CharelF01/RELIP-MODBUS-SMARTY/Code/RELIP-READER/SmartReader2_2023-Mar-29_07-19-46PM-000_CustomizedView1520858296_png.png

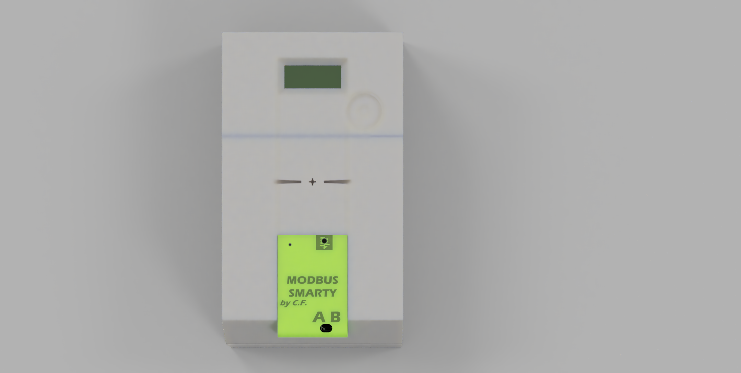
Code/RELIP-READER/SmartReader2_2023-Mar-29_07-19-46PM-000_CustomizedView1520858296_png.png
