CharelF01/RELIP-MODBUS-SMARTY/Photos/Smarty Modbus/IMG_20230321_090704.jpg

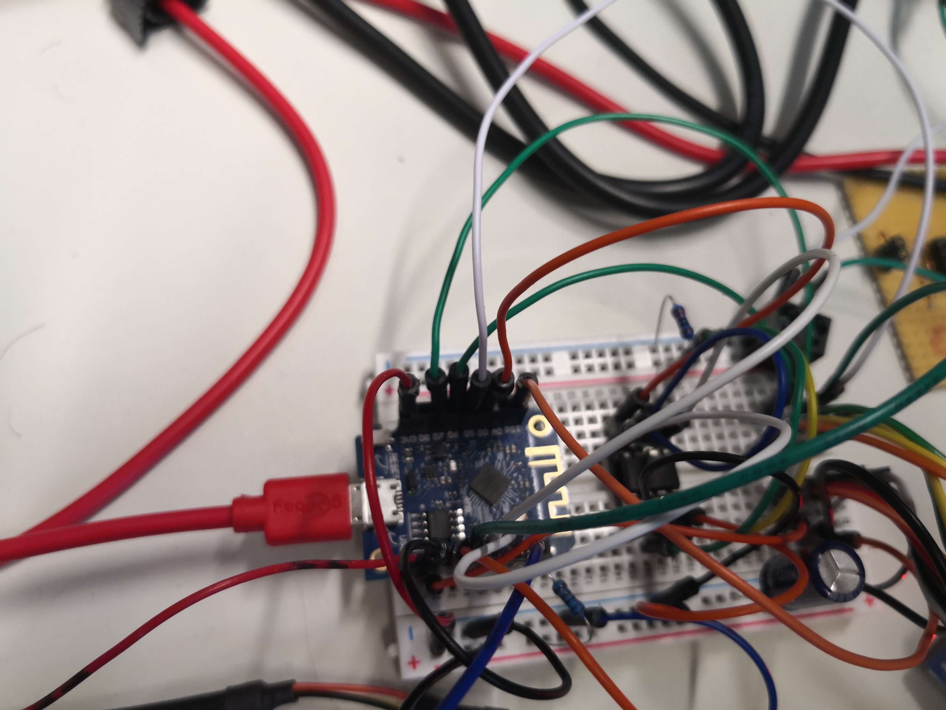
Photos/Smarty Modbus/IMG_20230321_090704.jpg
