CharelF01/RELIP-MODBUS-SMARTY/Photos/Smarty Modbus/IMG_20230321_090714.jpg

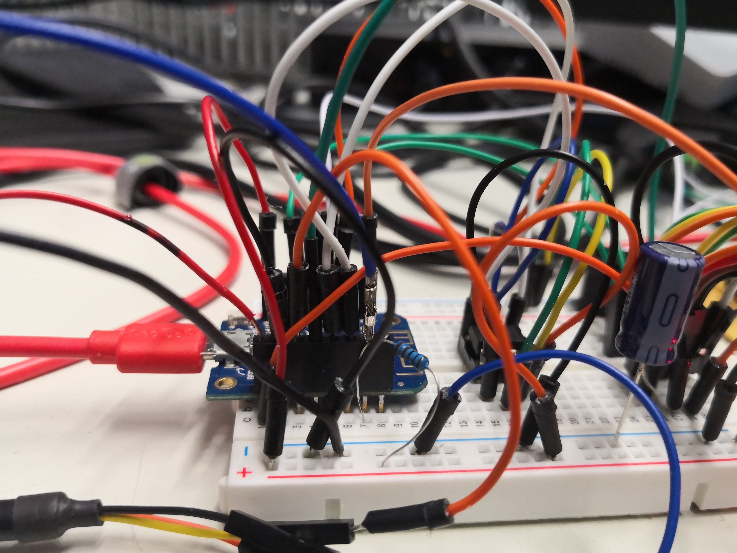
Photos/Smarty Modbus/IMG_20230321_090714.jpg
