CharelF01/RELIP-MODBUS-SMARTY/Photos/Smarty Modbus/IMG_20230323_114347.jpg

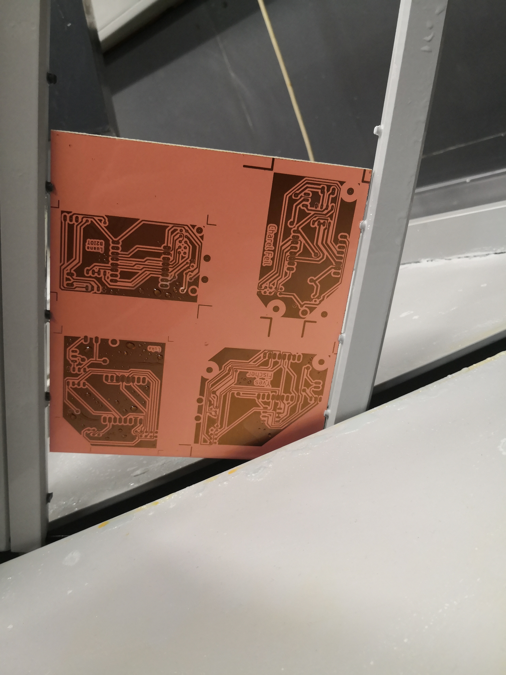
Photos/Smarty Modbus/IMG_20230323_114347.jpg
