CharelF01/RELIP-MODBUS-SMARTY/Photos/Smarty Modbus/IMG_20230323_133843.jpg

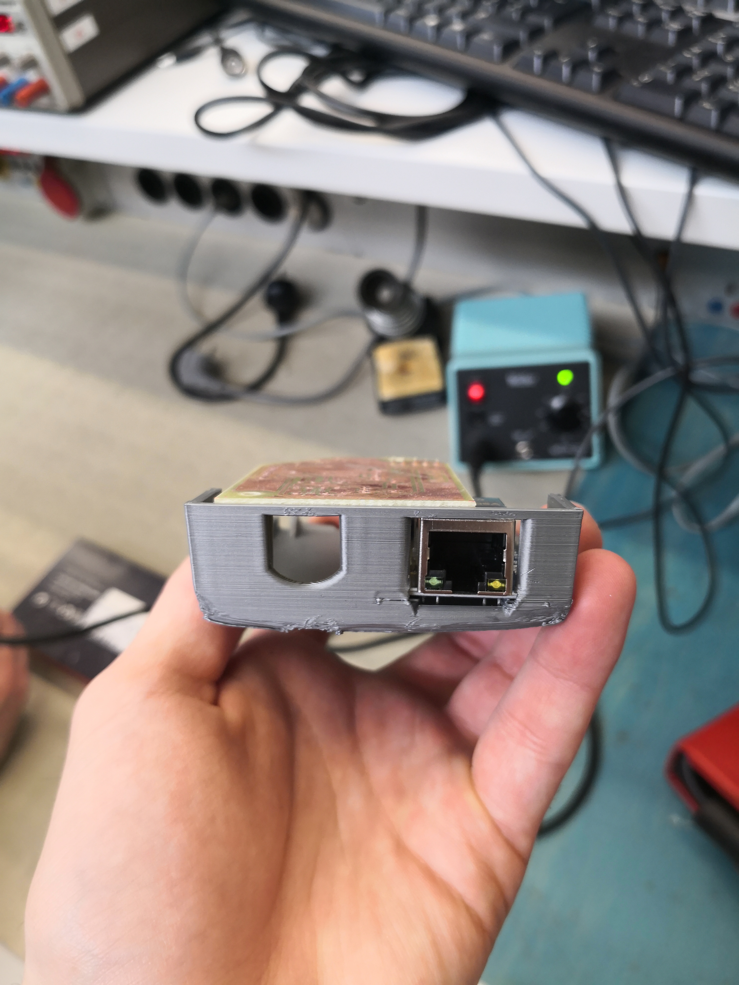
Photos/Smarty Modbus/IMG_20230323_133843.jpg
