CharelF01/RELIP-MODBUS-SMARTY/Photos/Smarty Modbus/IMG_20230324_115719.jpg

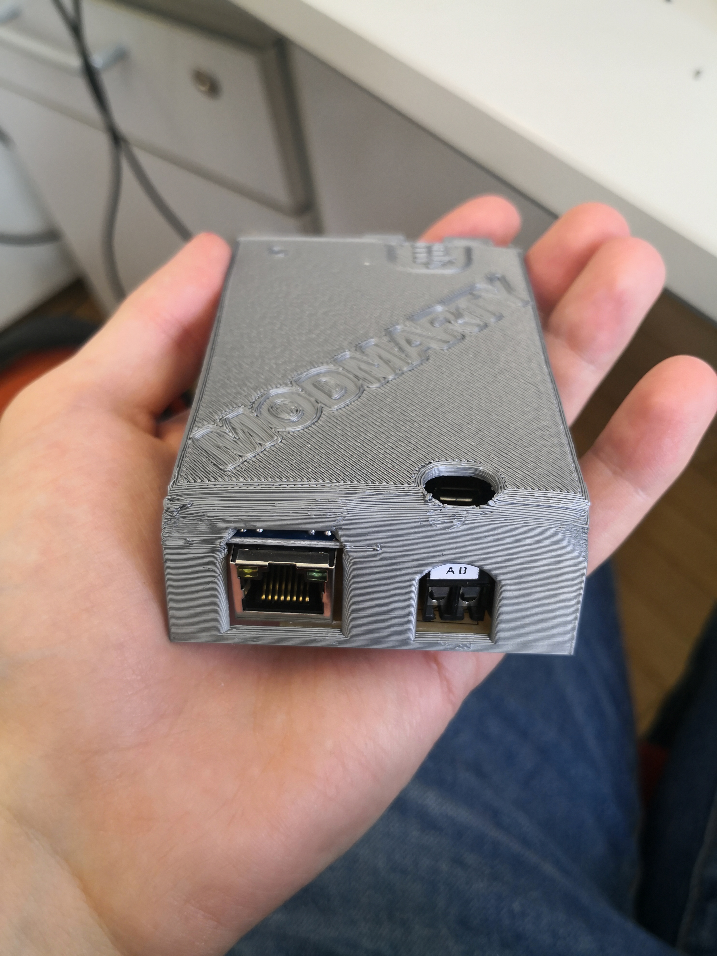
Photos/Smarty Modbus/IMG_20230324_115719.jpg
