CharelF01/RELIP-MODBUS-SMARTY/Photos/Smarty Modbus/IMG_20230324_115724.jpg

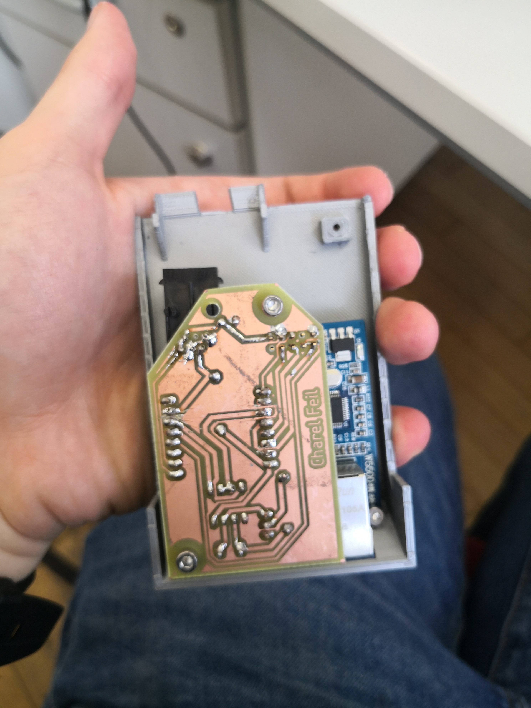
Photos/Smarty Modbus/IMG_20230324_115724.jpg
