CharelF01/RELIP-MODBUS-SMARTY/Photos/Smarty Modbus/IMG_20230329_201605.jpg

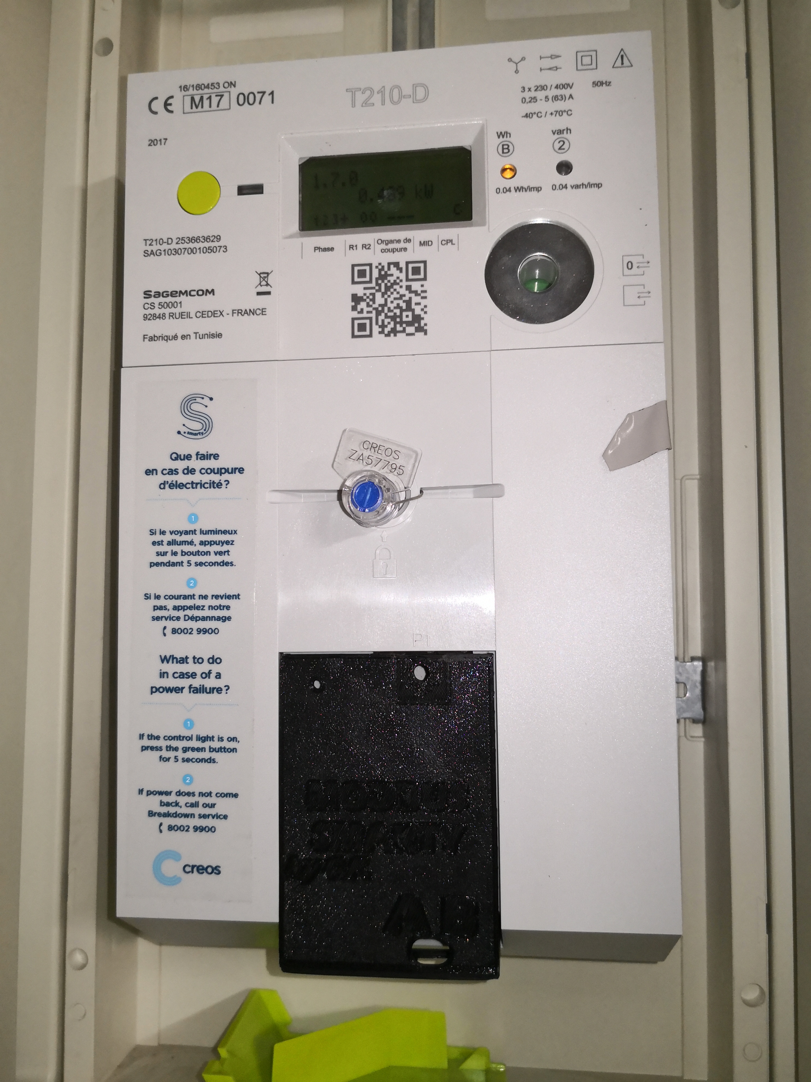
Photos/Smarty Modbus/IMG_20230329_201605.jpg
