CharelF01/RELIP-MODBUS-SMARTY/Photos/Smarty Modbus/IMG_20230329_201856.jpg

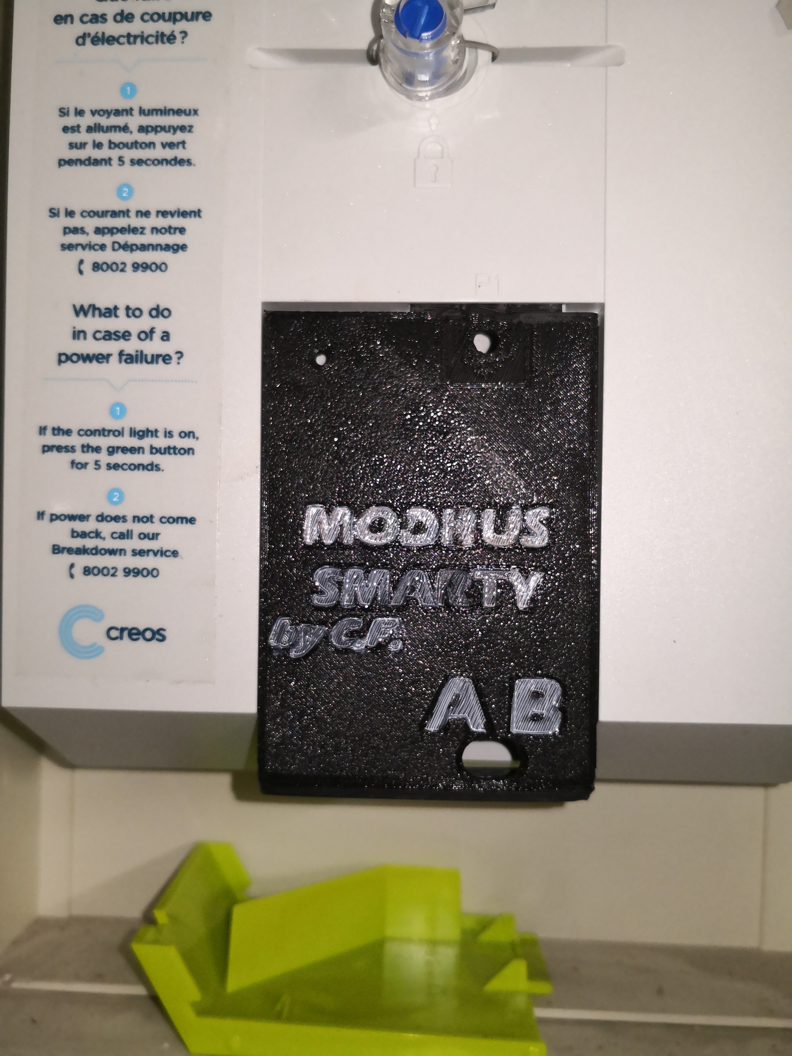
Photos/Smarty Modbus/IMG_20230329_201856.jpg
