CharelF01/RELIP-MODBUS-SMARTY/Photos/Smarty Simulator/IMG_20230223_134645.jpg

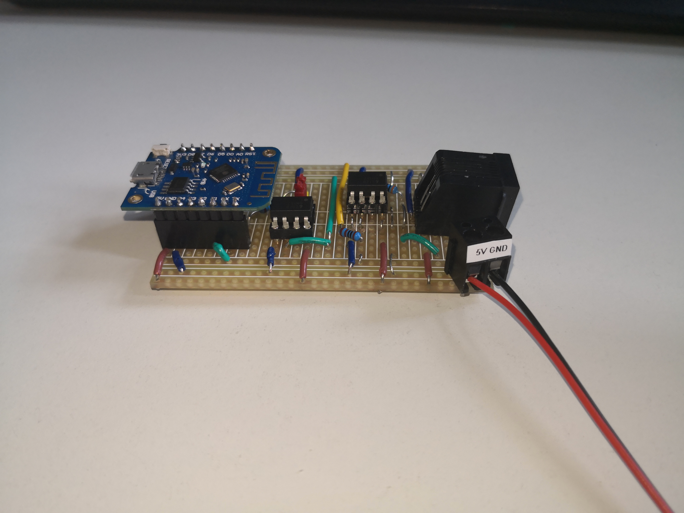
Photos/Smarty Simulator/IMG_20230223_134645.jpg
