CharelF01/RELIP-MODBUS-SMARTY/Photos/Smarty Simulator/IMG_20230223_134919.jpg

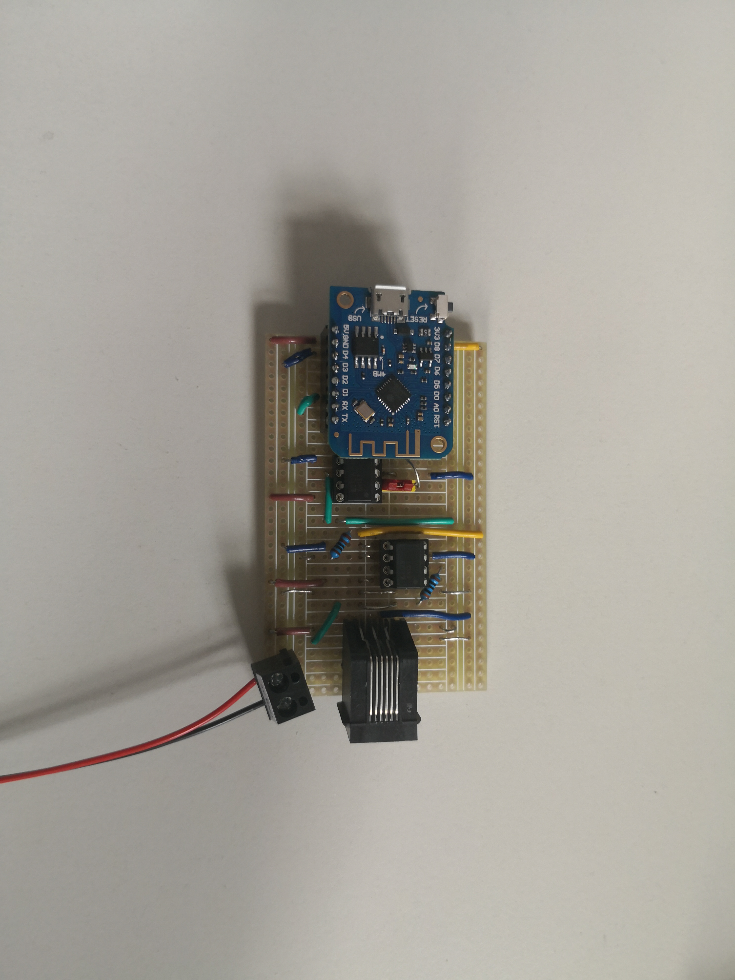
Photos/Smarty Simulator/IMG_20230223_134919.jpg
