CharelF01/RELIP-MODBUS-SMARTY/Photos/Smarty Simulator/IMG_20230223_135027.jpg

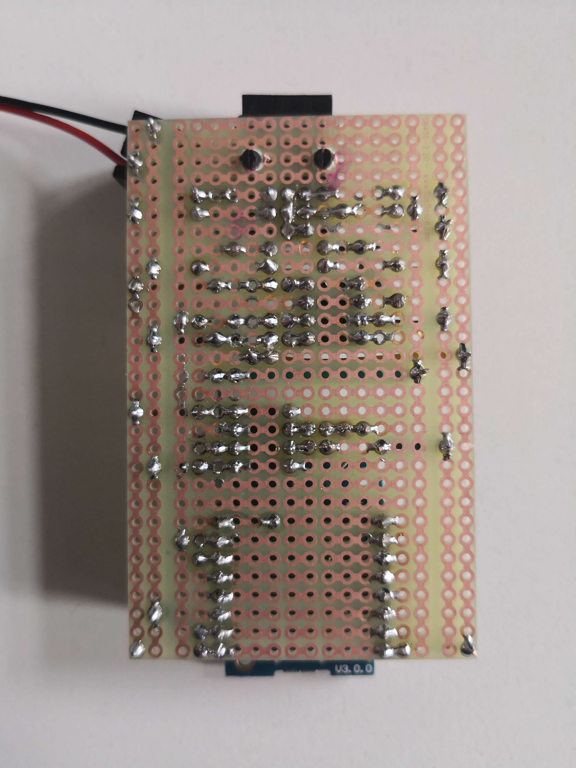
Photos/Smarty Simulator/IMG_20230223_135027.jpg
