CharelF01/RELIP-MODBUS-SMARTY/Photos/Smarty Simulator/IMG_20230223_135046.jpg

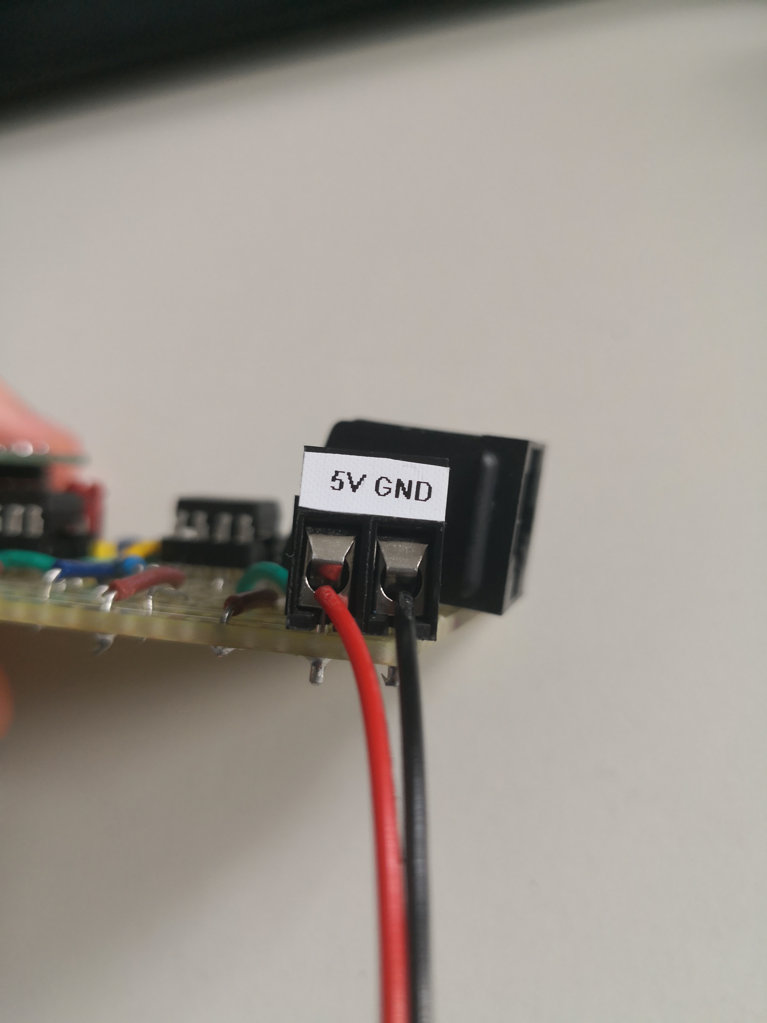
Photos/Smarty Simulator/IMG_20230223_135046.jpg
