CharelF01/RELIP-MODBUS-SMARTY/Photos/Smarty Simulator/IMG_20230223_135050.jpg

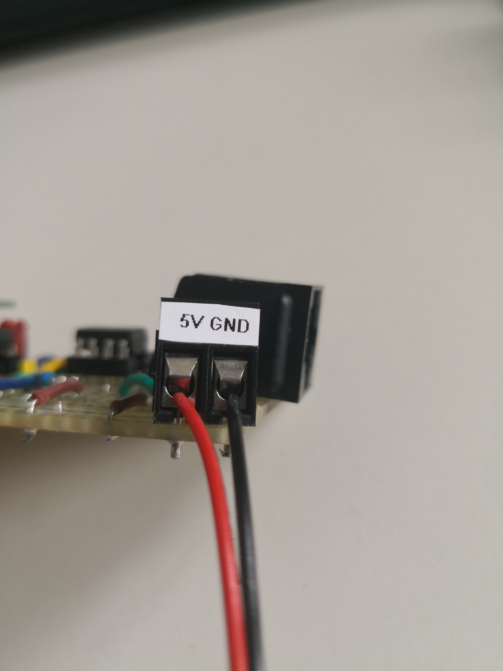
Photos/Smarty Simulator/IMG_20230223_135050.jpg
