CharelF01/RELIP-MODBUS-SMARTY/Photos/view on screen from data/IMG_20230223_152047.jpg

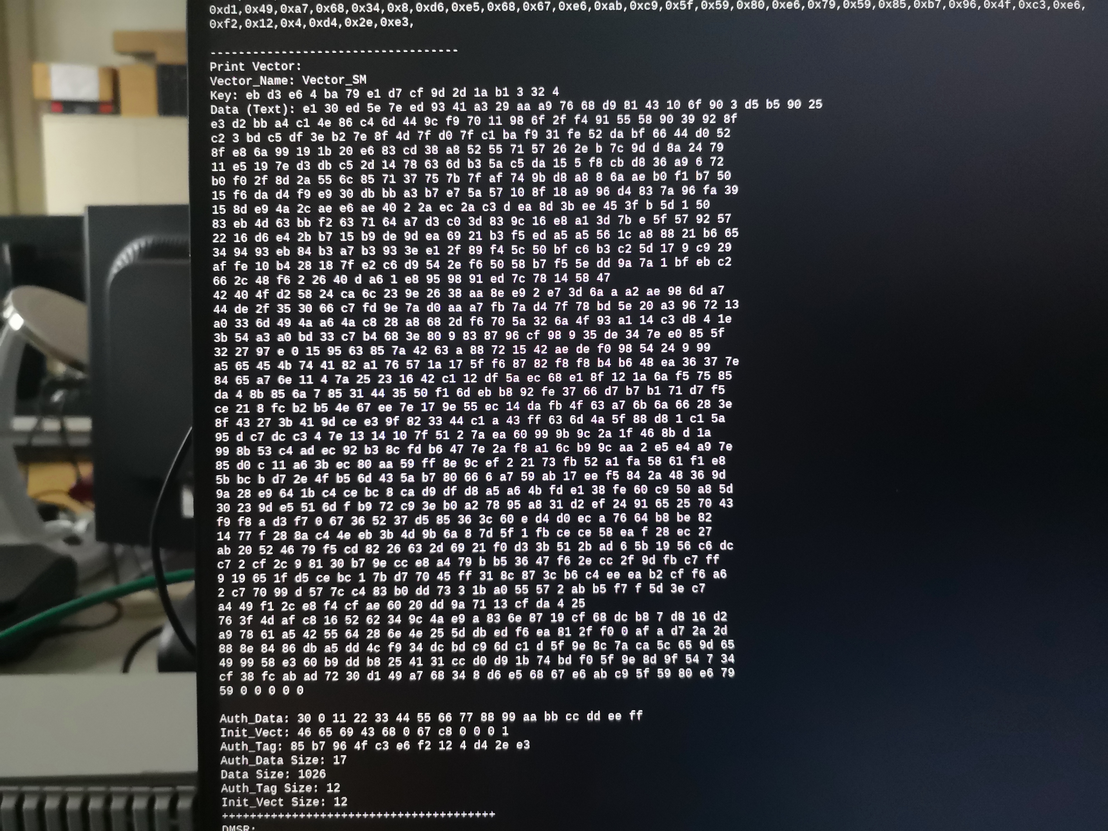
Photos/view on screen from data/IMG_20230223_152047.jpg
