CharelF01/RELIP-MODBUS-SMARTY/Photos/view on screen from data/IMG_20230223_152058.jpg

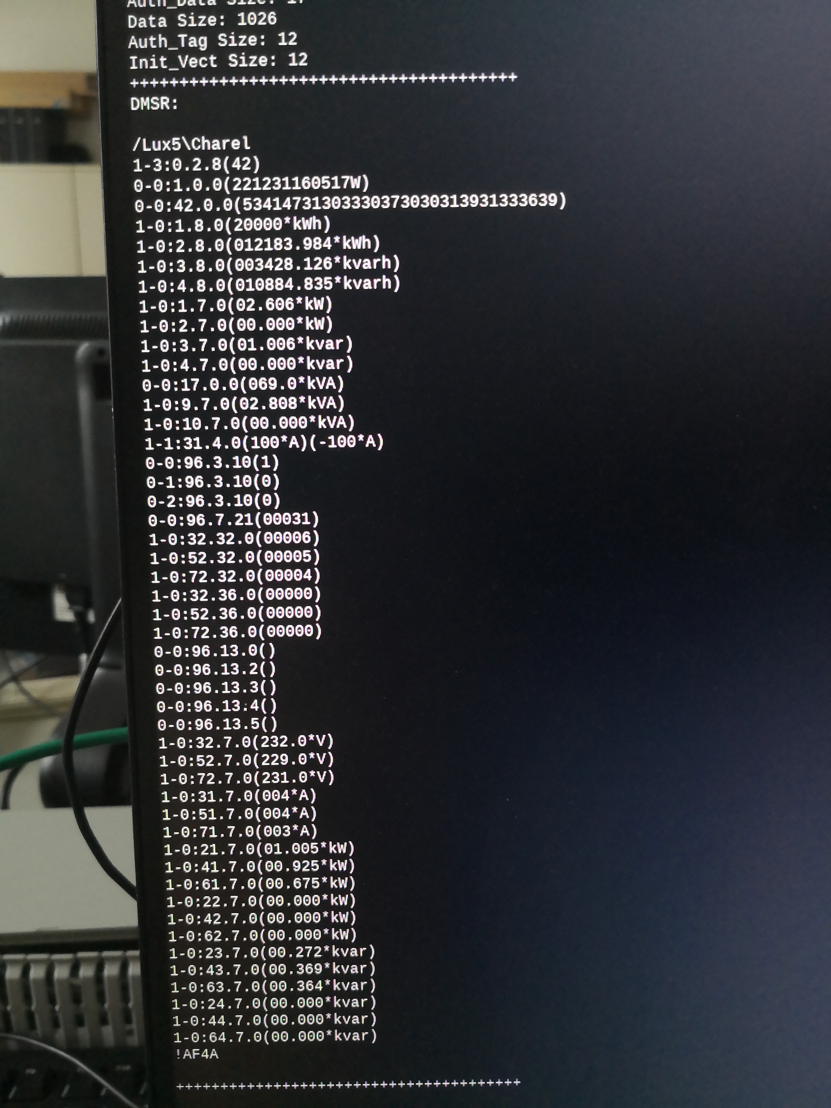
Photos/view on screen from data/IMG_20230223_152058.jpg
